CTDL/museduino/hardware/expresspcb/1.7/museduino-schematic-v1-7-smorgasboard.pdf

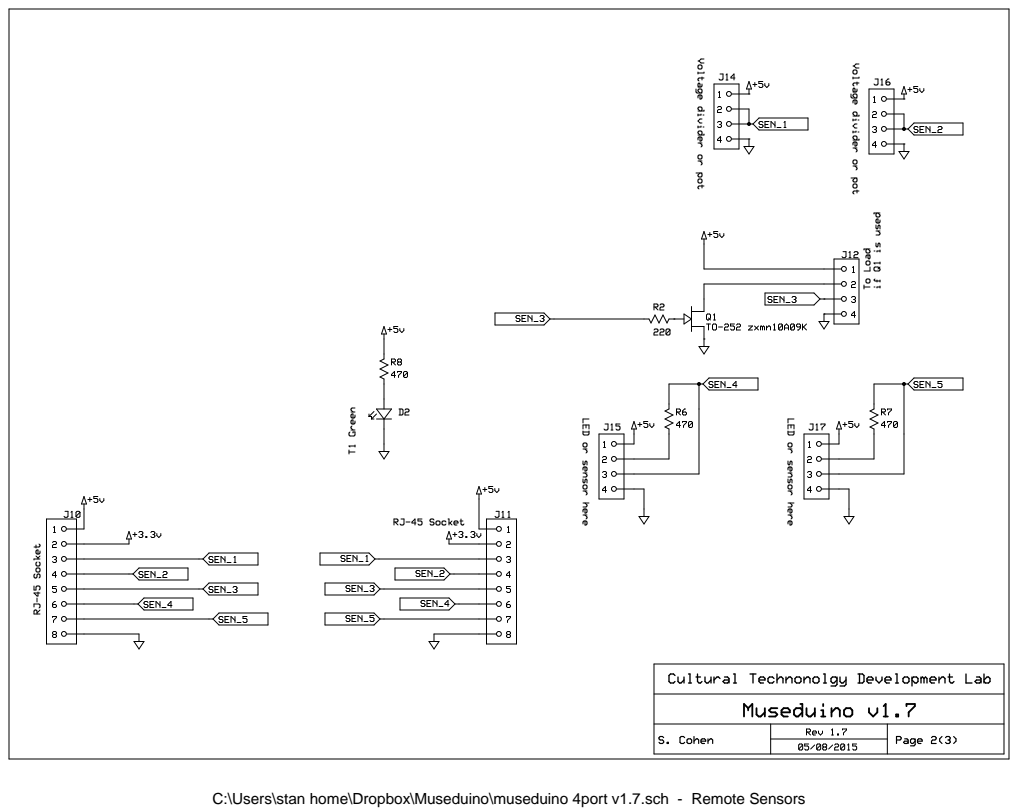
[picture p12: page 1]

C:\Users\stan home\Dropbox\Museduino\museduino 4port v1.7.sch - Remote Sensors
