CTDL/museduino/hardware/expresspcb/2.0/museduino-schematic-v2.0-extpower.pdf

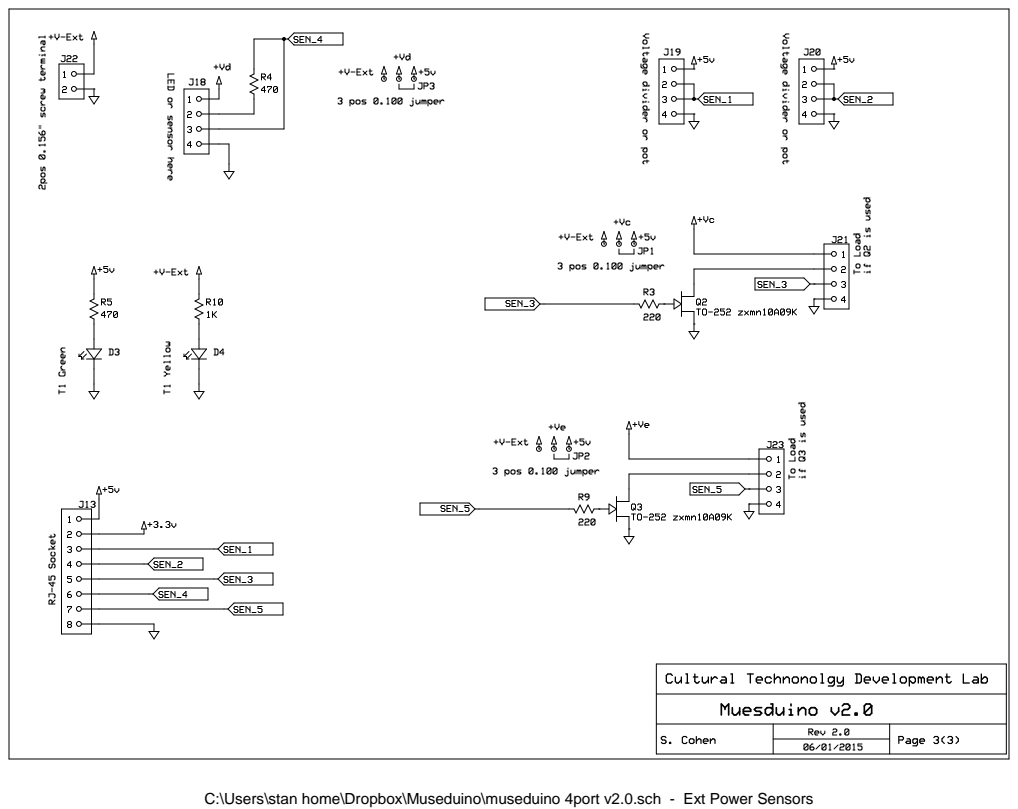
[picture p16: page 1]

C:\Users\stan home\Dropbox\Museduino\museduino 4port v2.0.sch - Ext Power Sensors
