CTDL/museduino/hardware/expresspcb/2.0/museduino-schematic-v2.0-smorgasboard.pdf

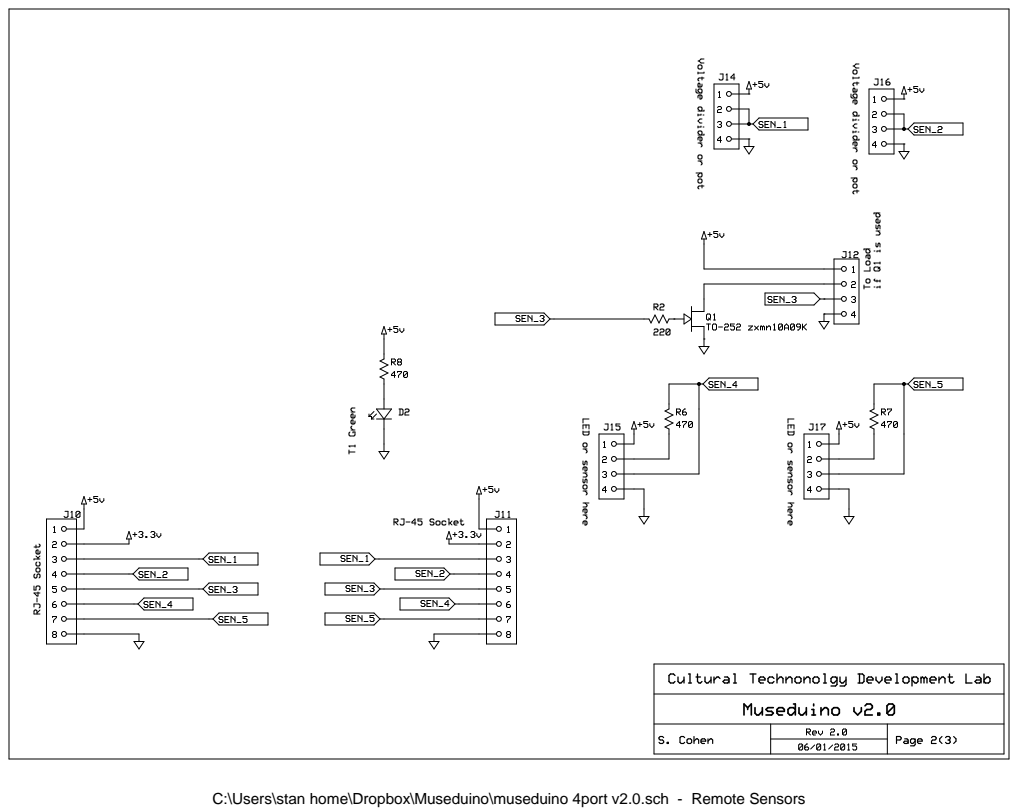
[picture p17: page 1]

C:\Users\stan home\Dropbox\Museduino\museduino 4port v2.0.sch - Remote Sensors
