CTDL/museduino/hardware/expresspcb/2.2/museduino_pcb_layout_v2-2a.pdf

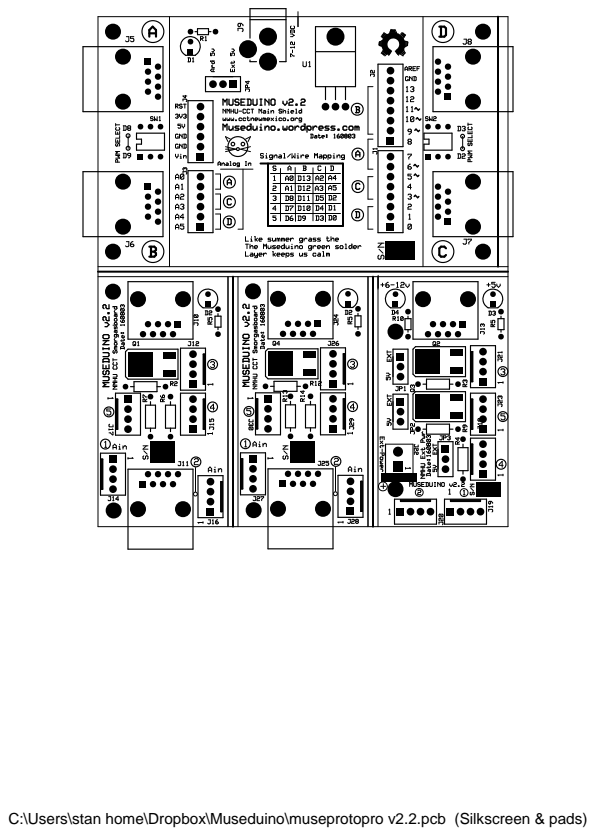
[picture p18: page 1]

C:\Users\stan home\Dropbox\Museduino\museprotopro v2.2.pcb (Silkscreen & pads)
