CTDL/museduino/hardware/expresspcb/1.0/museduino-schematic-v1-mainshield.pdf

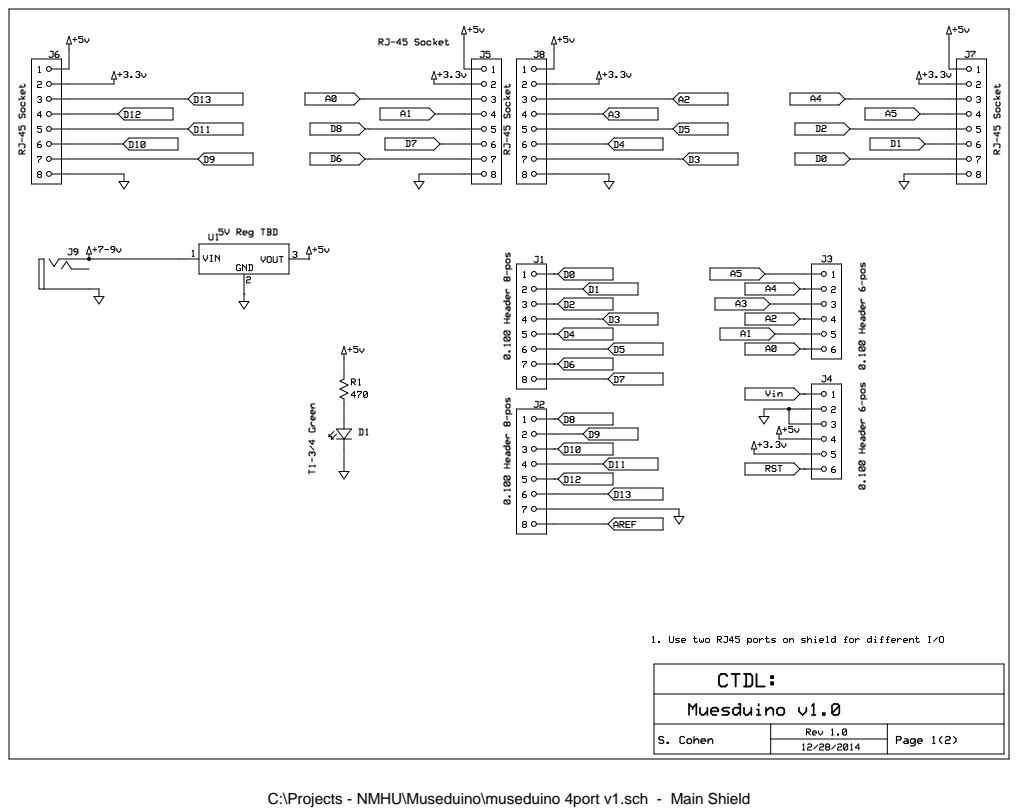
[picture p23: page 1]

C:\Projects - NMHU\Museduino\museduino 4port v1.sch - Main Shield
