CTDL/museduino/hardware/expresspcb/1.5/Museduino Schematic v1.5 main.pdf

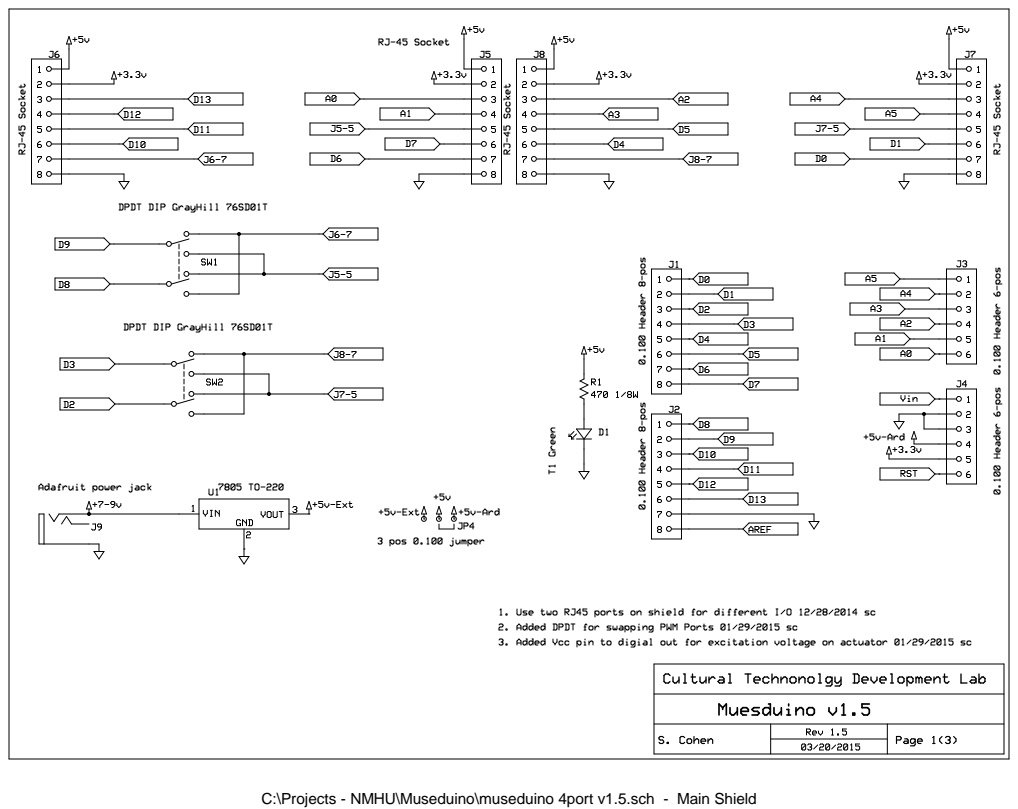
[picture p24: page 1]

C:\Projects - NMHU\Museduino\museduino 4port v1.5.sch - Main Shield
