CTDL/museduino/hardware/expresspcb/2.0/museduino-schematic-v2.0-main.pdf

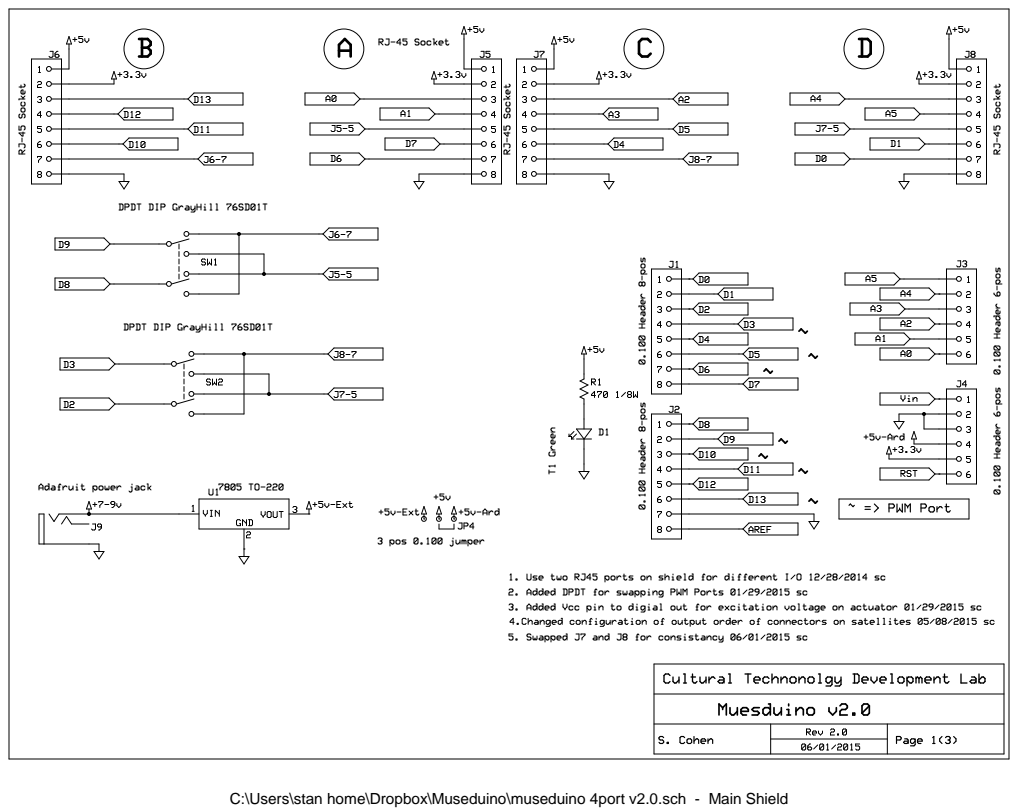
[picture p25: page 1]

C:\Users\stan home\Dropbox\Museduino\museduino 4port v2.0.sch - Main Shield
