CTDL/museduino/hardware/kicad/SMORGASBOARD/3.0.1/Muse_smorgas_v3.0.1-screwterminal/smorgsboard_3.0.1-pcb.pdf

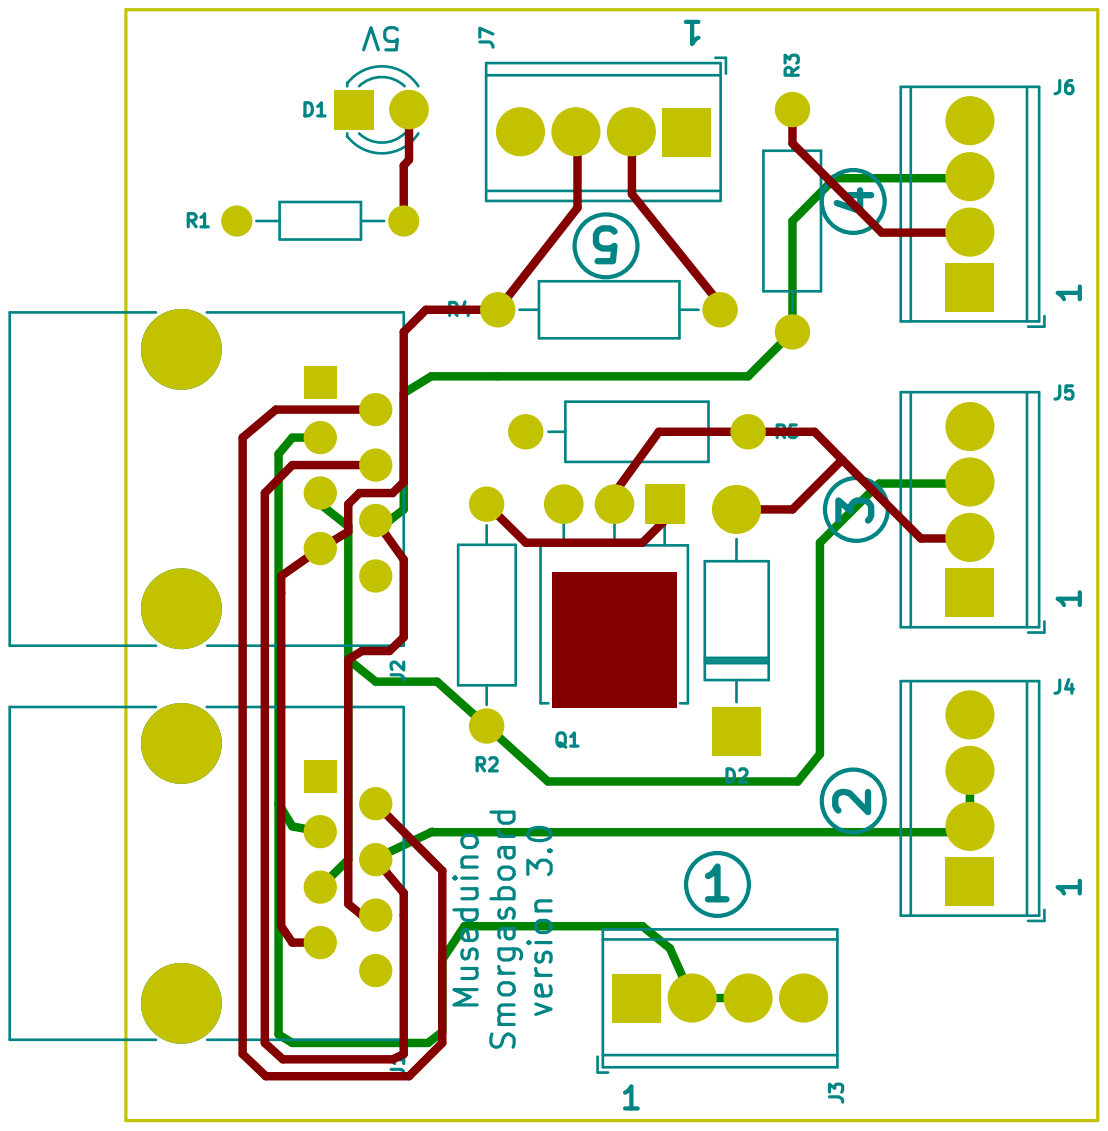
[picture p26: page 1]
