CTDL/museduino/hardware/kicad/MAIN SHIELD/4.0.2/MUSE_main_4.0.2/MUSE_main_4.0.2-schematic.pdf

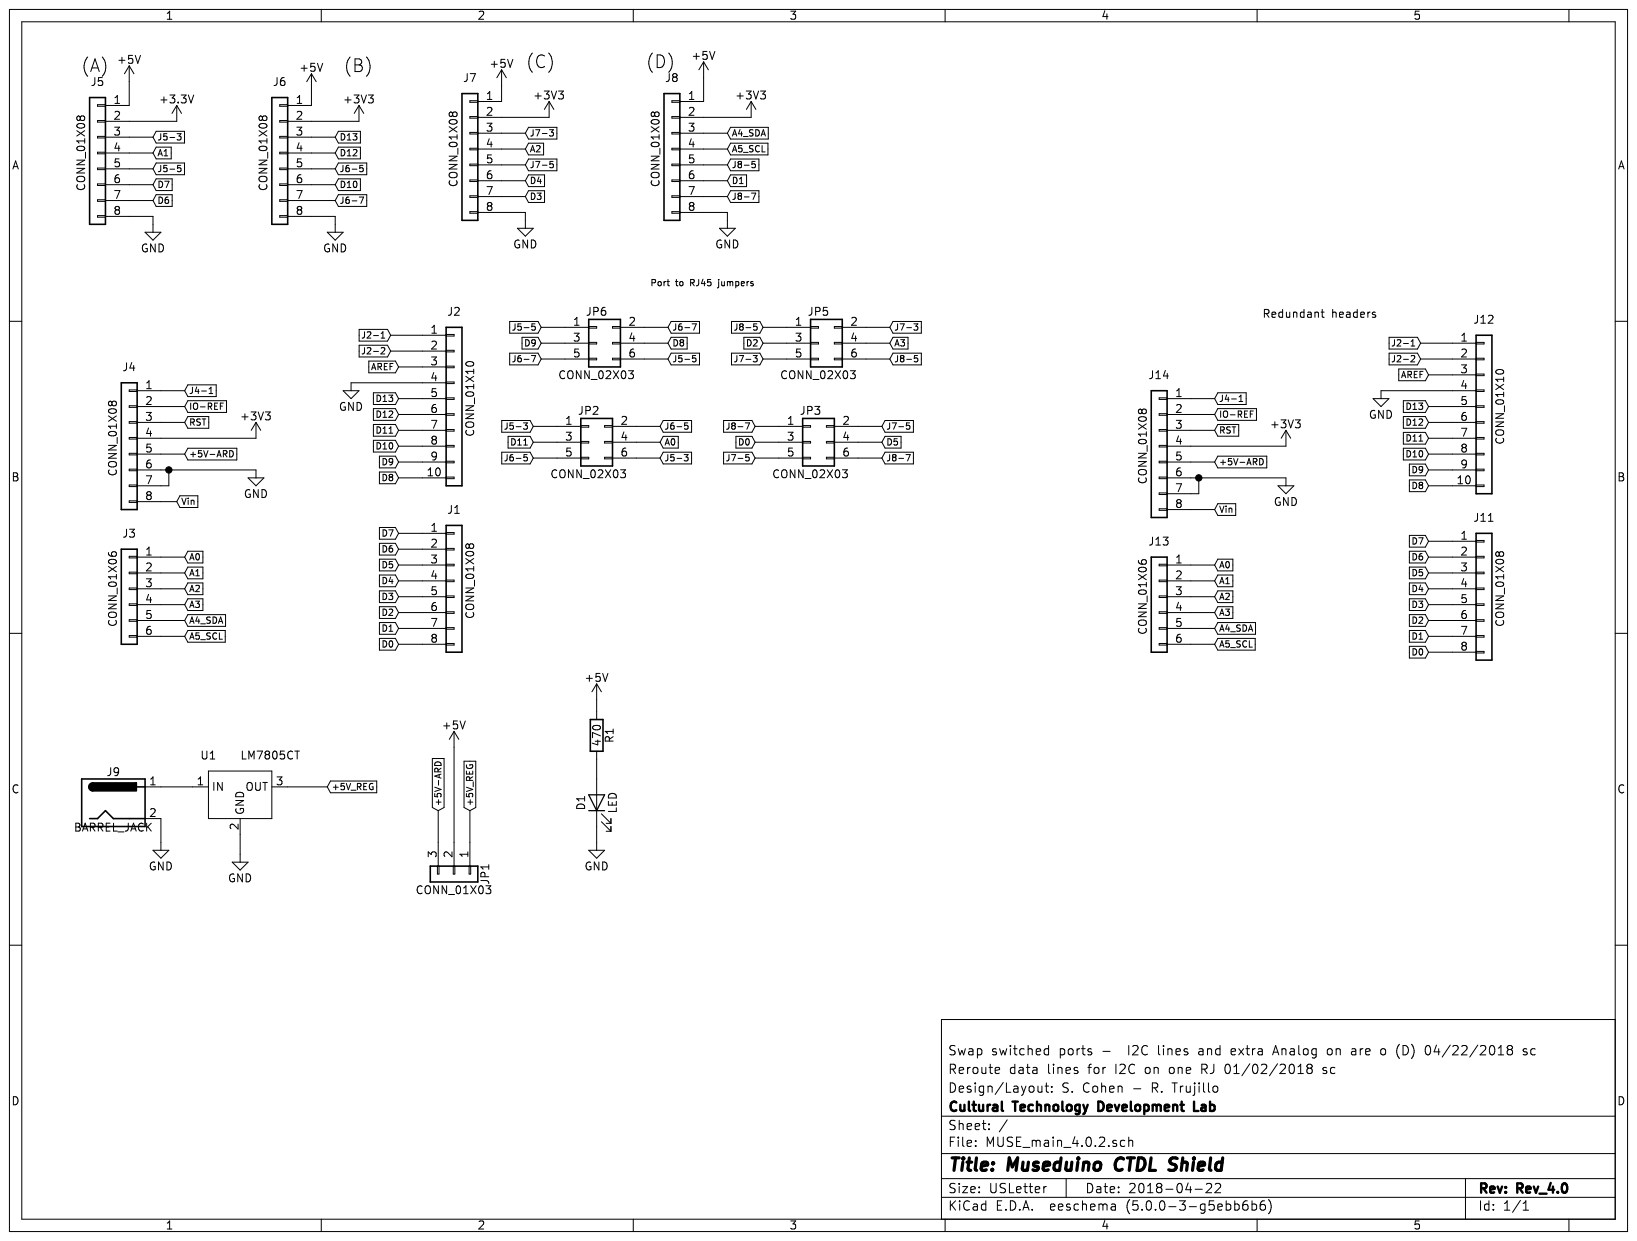
[picture p27: page 1]
