CTDL/museduino/hardware/kicad/EXTERNAL POWER BOARD/3.0.2/Muse_ext_pow_v3.0.2_screwterminal/museduino_extpower_3.0.2.pdf

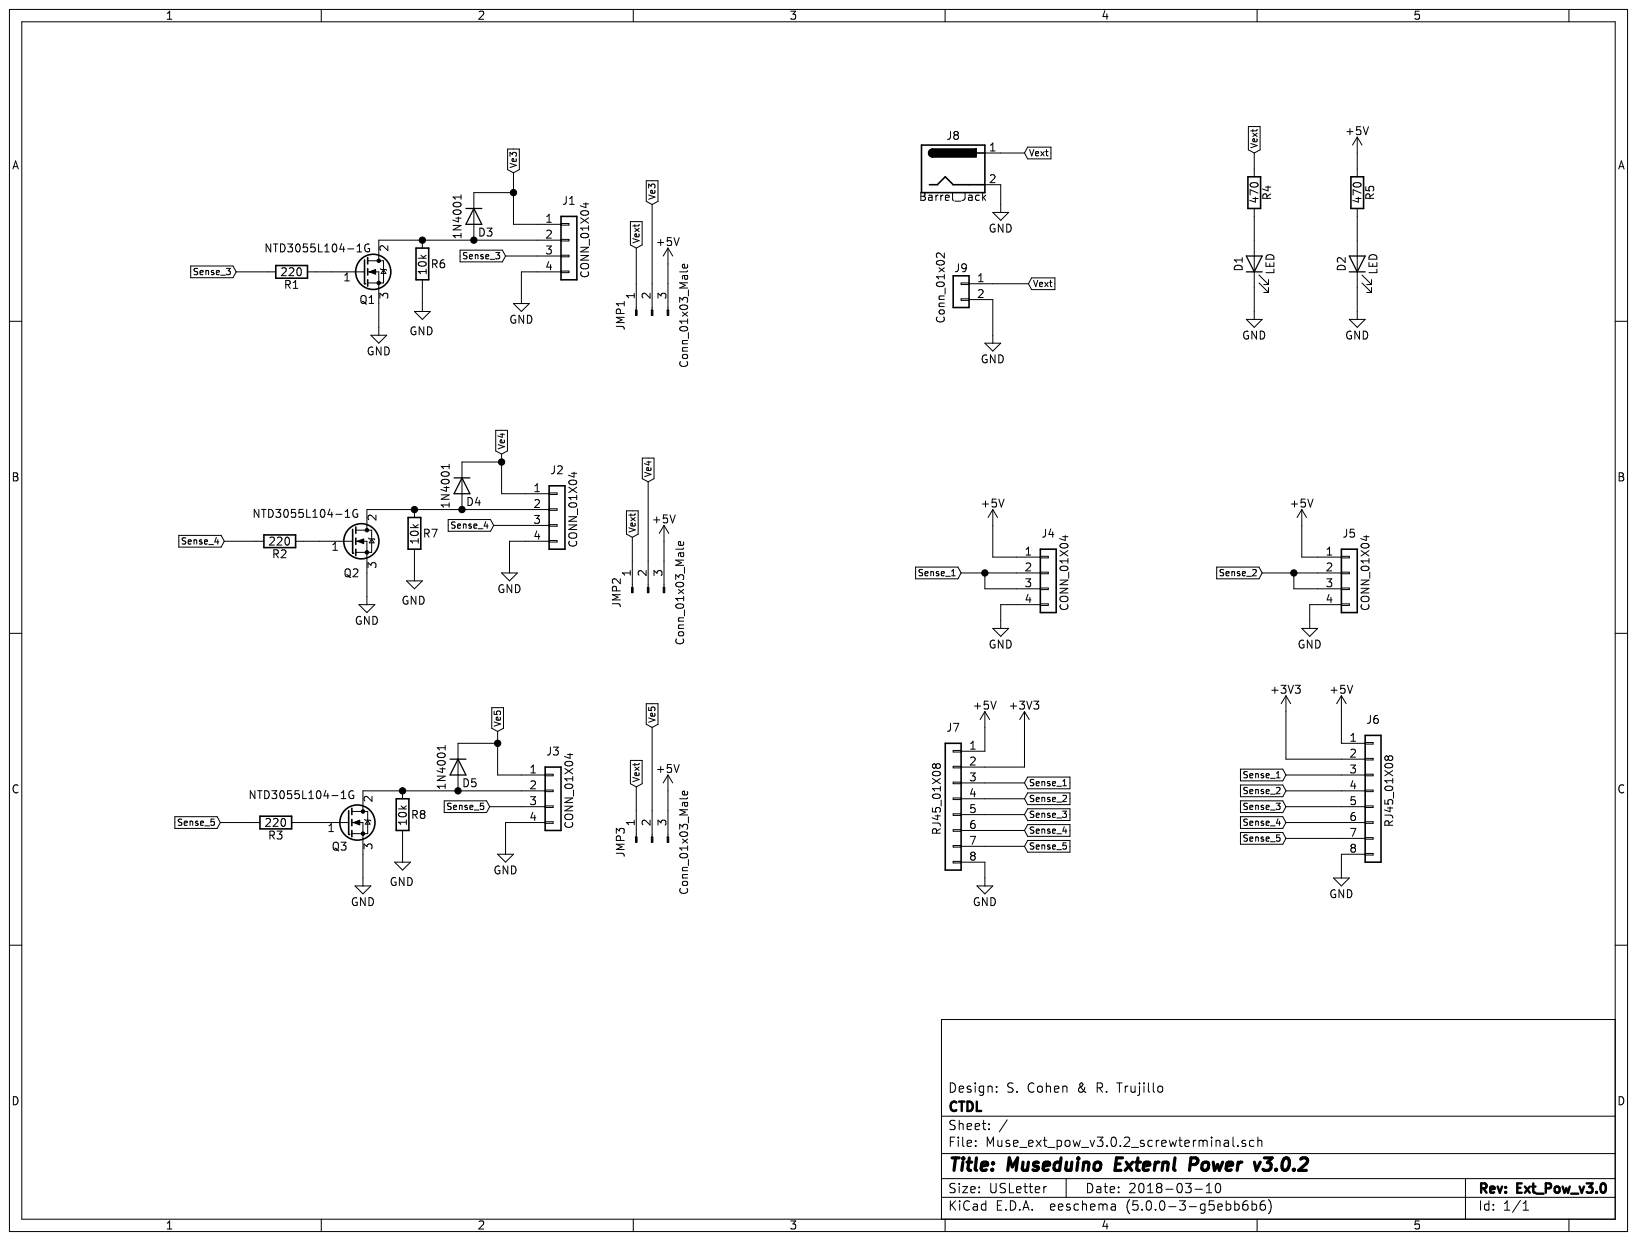
[picture p28: page 1]
