CTDL/museduino/hardware/kicad/PORT EXTENDER/1.0.6/MUSE_port_ext_1.0.6/MUSE_port_ext_1.0.6-pcb.pdf

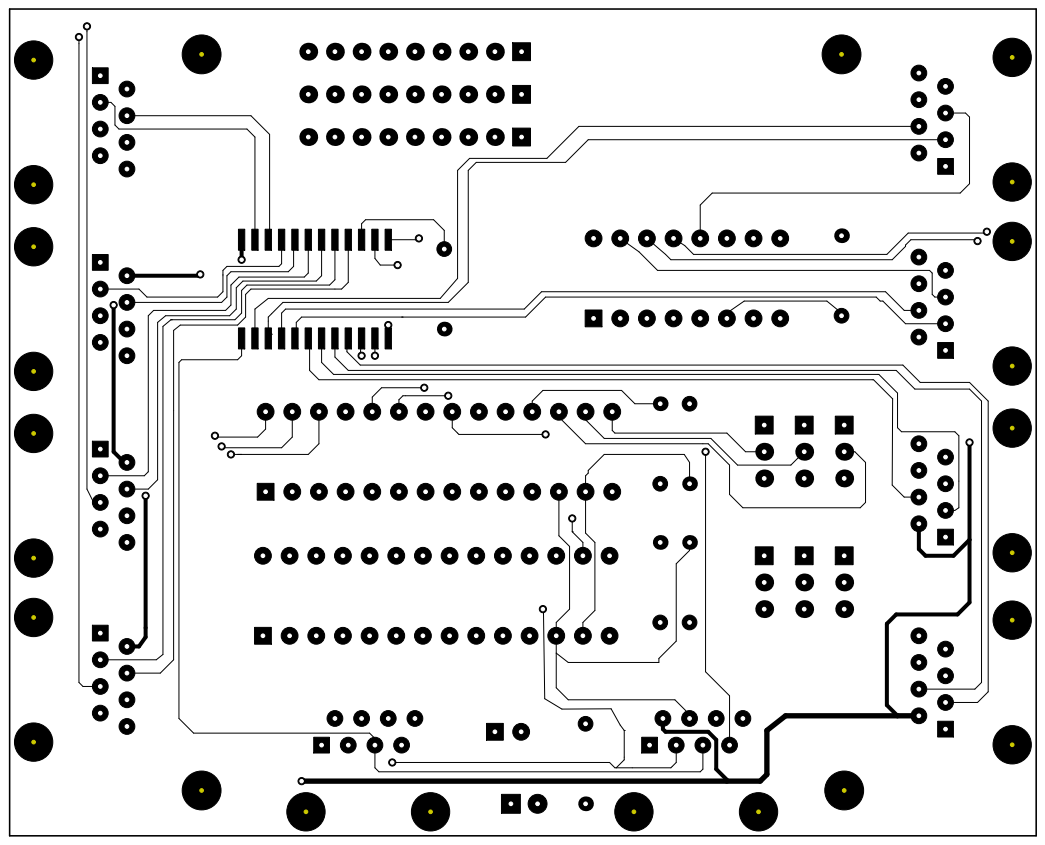
[picture p29: page 1]

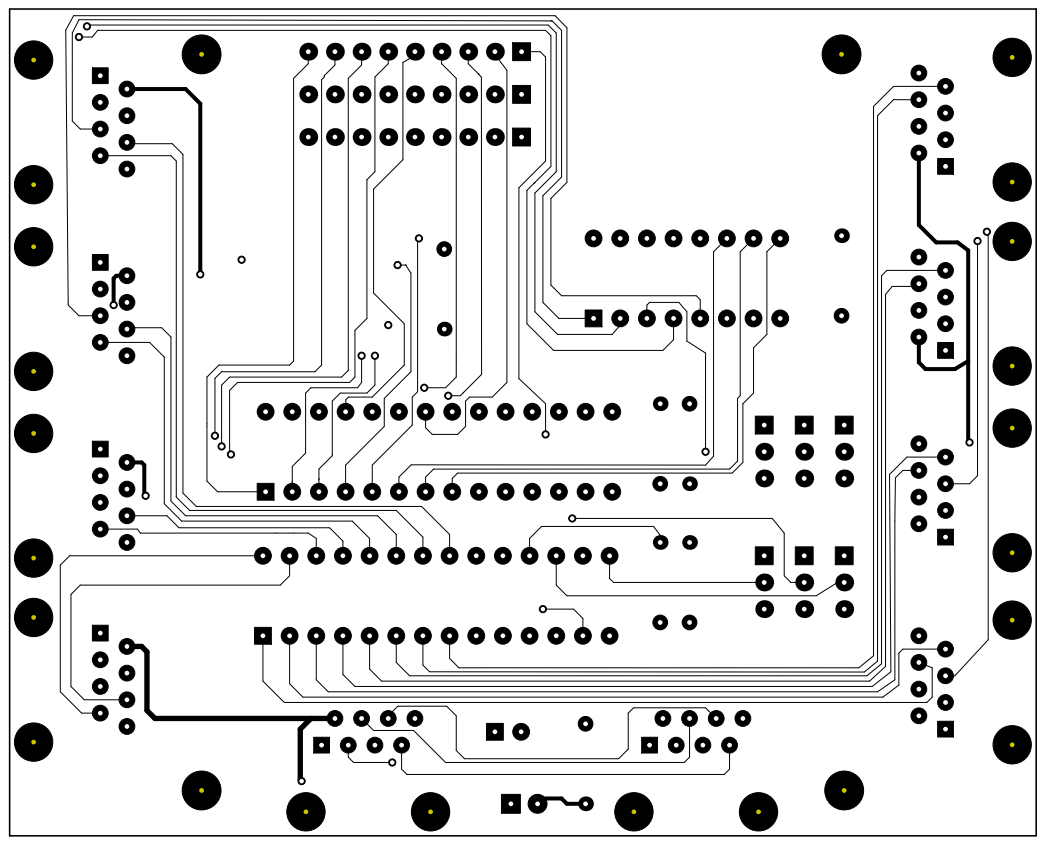
[picture p30: page 2]

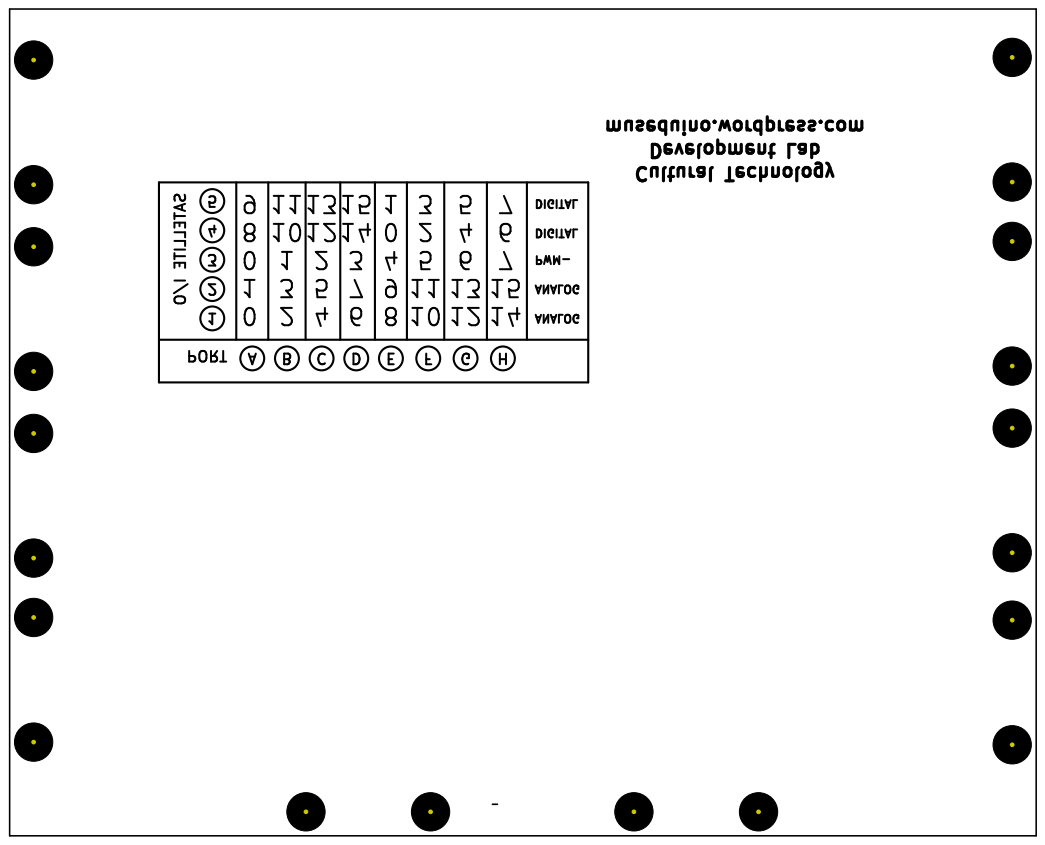
[picture p31: page 3]

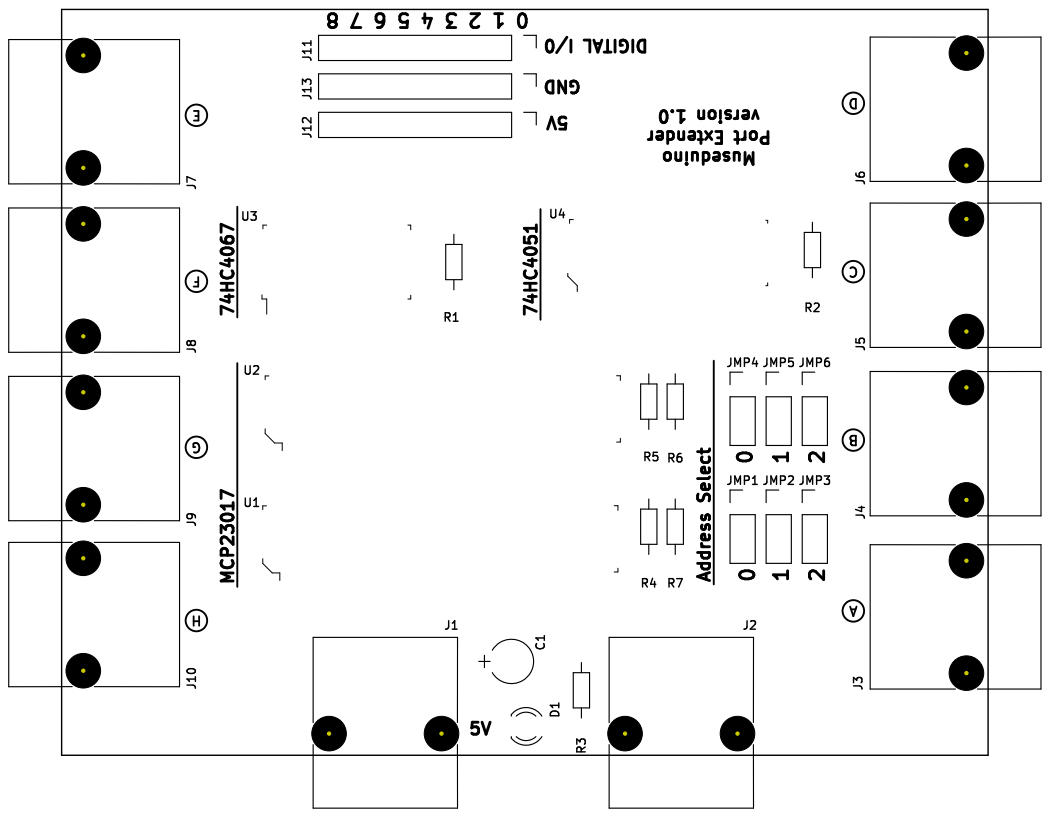
[picture p32: page 4]
