CTDL/museduino/hardware/kicad/PORT EXTENDER/1.0.6/MUSE_port_ext_1.0.6/MUSE_port_ext_1.0.6-schematic.pdf

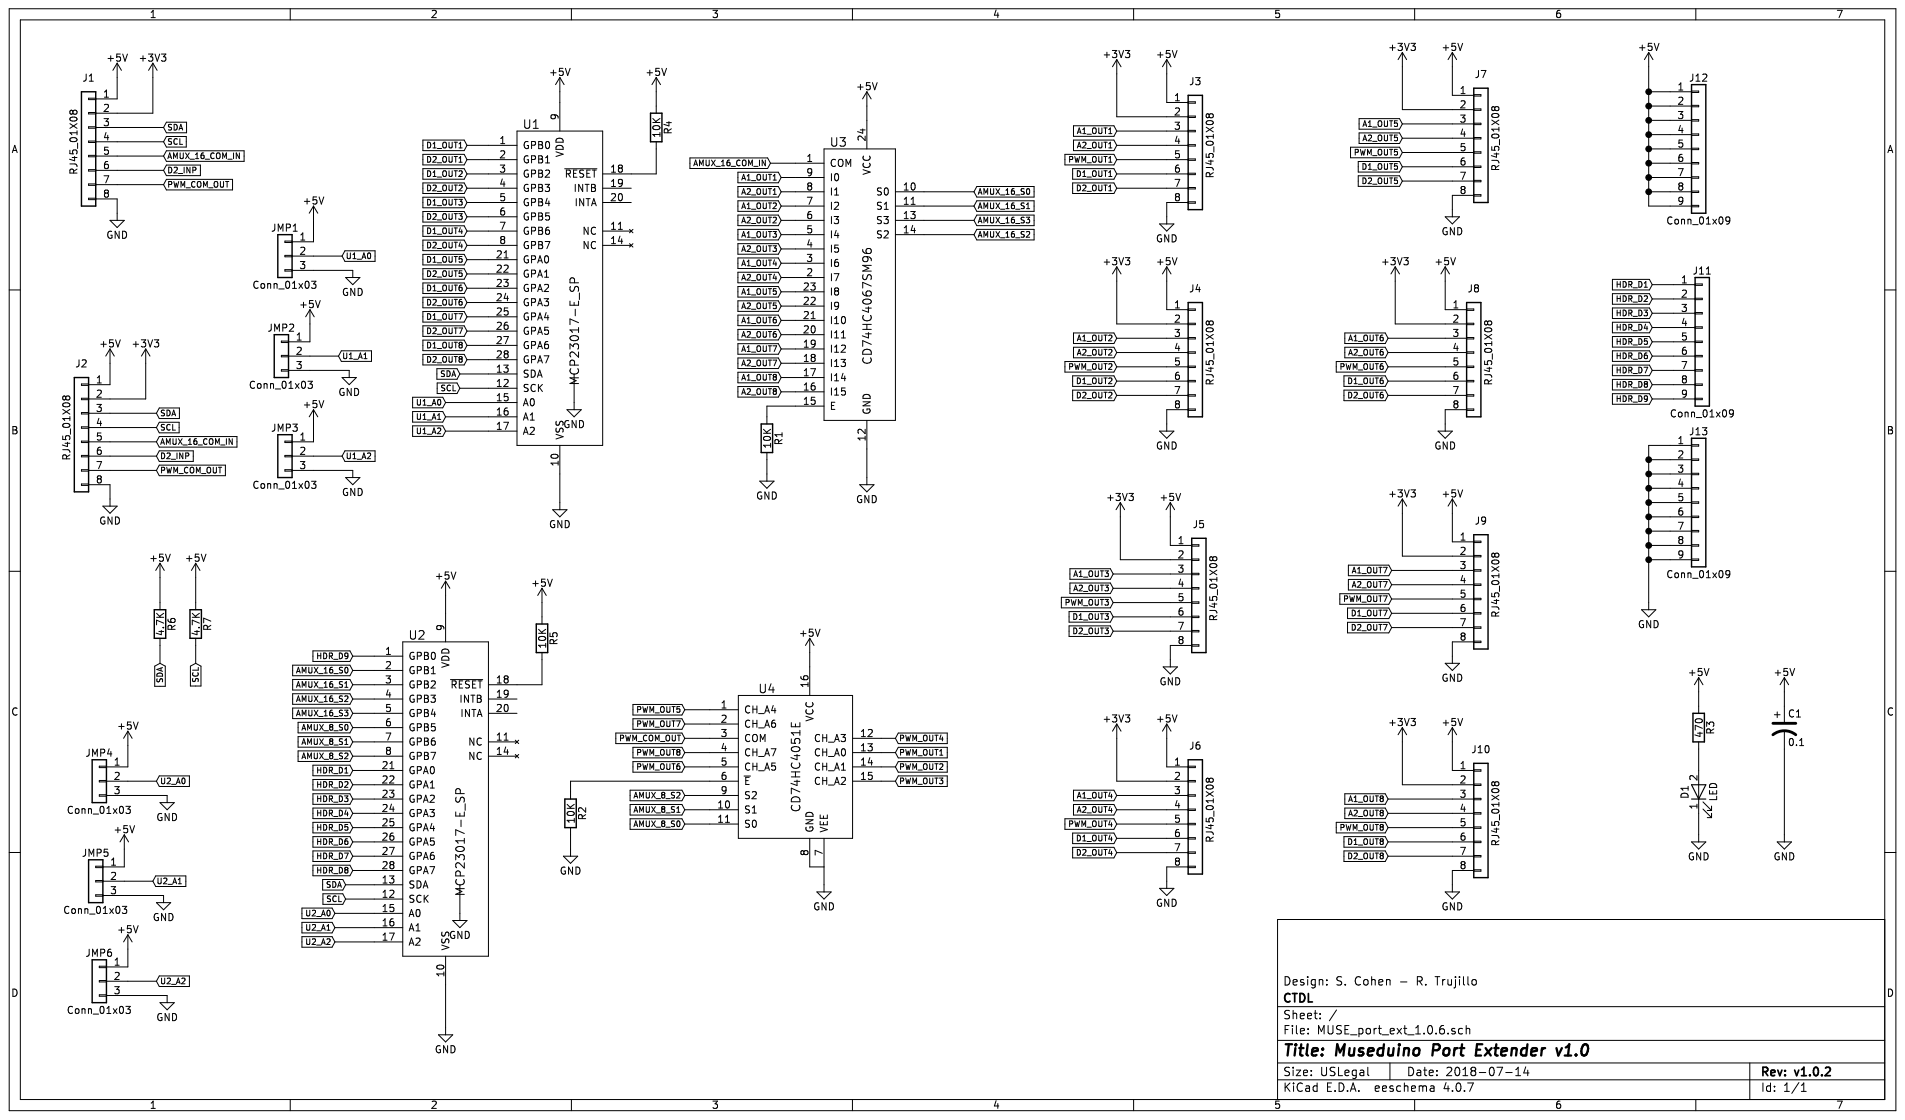
[picture p33: page 1]
