CTDL/museduino/hardware/kicad/SMORGASBOARD/3.0.1/Muse_smorgas_v3.0.1-screwterminal/smorgsboard_3.0.1-schematic.pdf

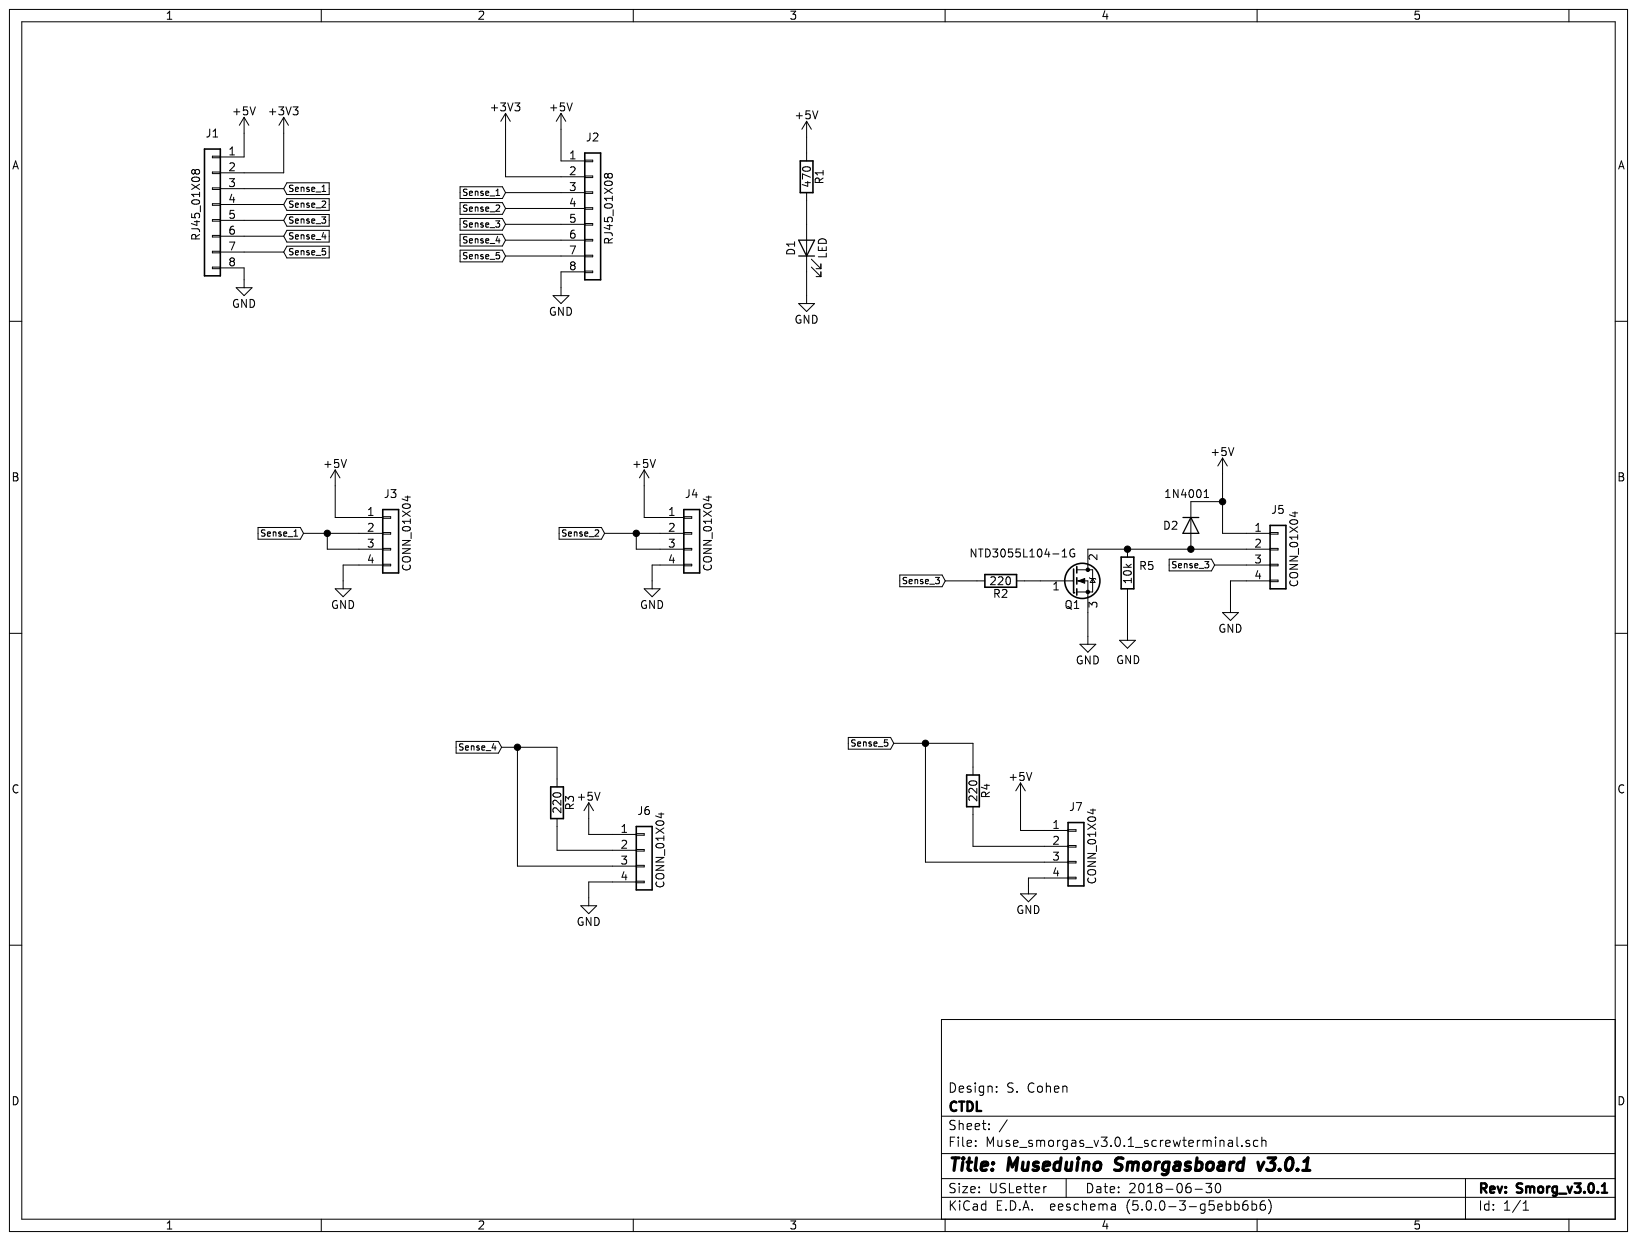
[picture p34: page 1]
